alx-uta/RC-Transmitter/3D/STEP/Battery/BatteryCover.step

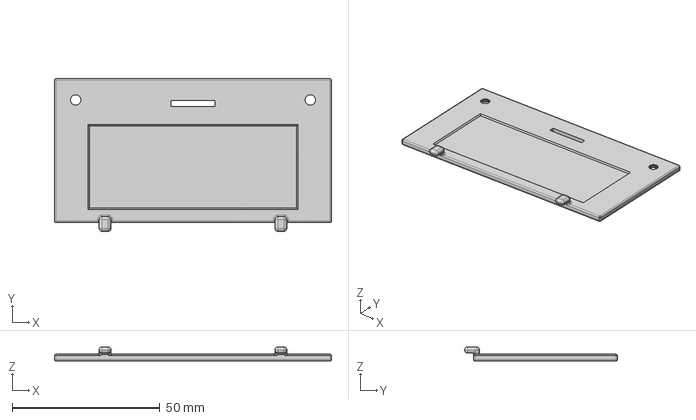
[picture p15: CAD file, 2024-01-06]
3D/STEP/Battery/BatteryCover.step
93.7 x 51.7 x 4.85 mm
