alx-uta/RC-Transmitter/3D/STEP/Battery/21700_BatteryHolder.step

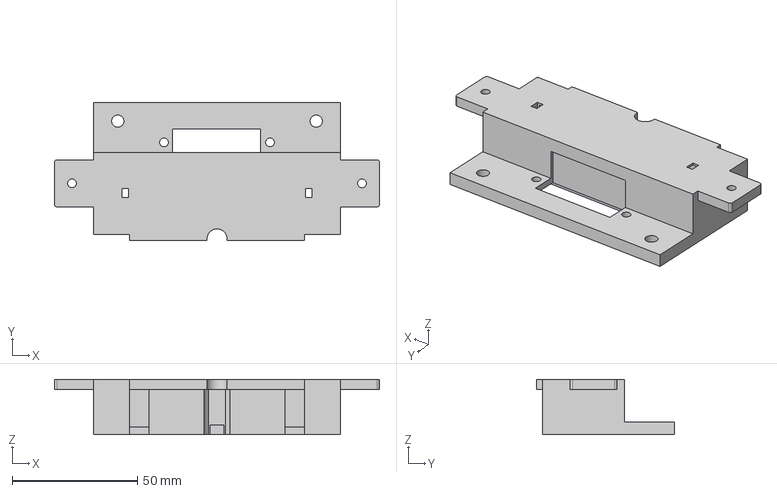
[picture p16: CAD file, 2024-01-06]
3D/STEP/Battery/21700_BatteryHolder.step
130.0 x 55.0 x 22.0 mm
