alx-uta/RC-Transmitter/3D/STEP/Battery/18650_BatteryHolderSpacer.step

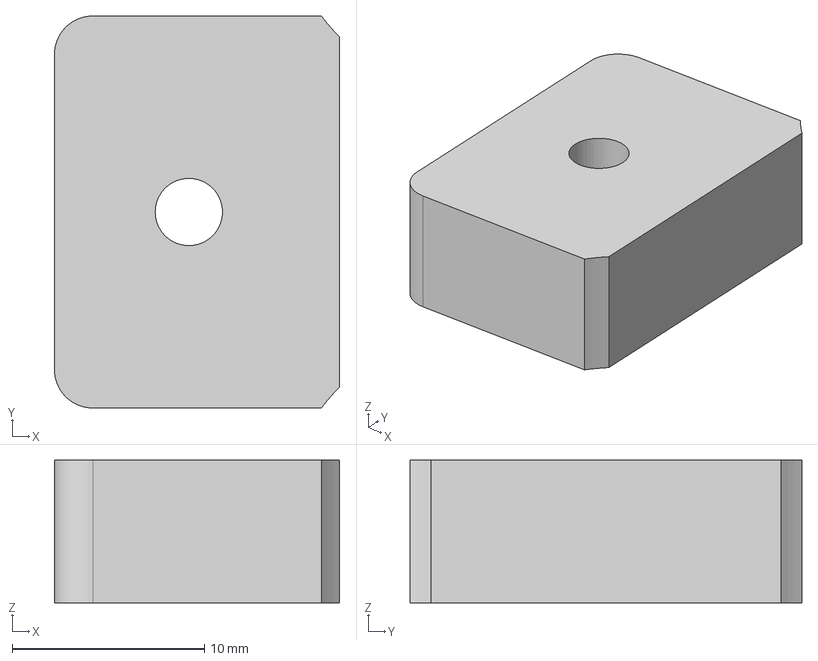
[picture p17: CAD file, 2024-01-06]
3D/STEP/Battery/18650_BatteryHolderSpacer.step
14.8 x 20.4 x 7.44 mm
