alx-uta/RC-Transmitter/3D/STEP/Battery/18650_BatteryHolder.step

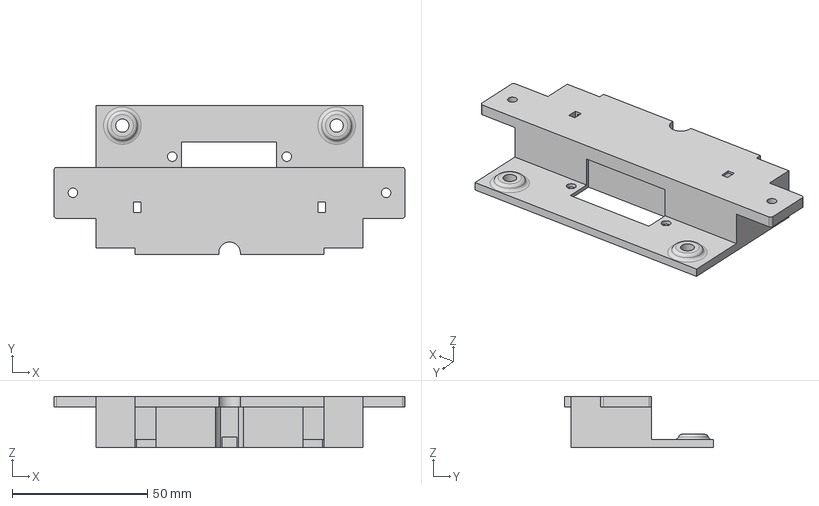
[picture p18: CAD file, 2024-01-06]
3D/STEP/Battery/18650_BatteryHolder.step
130.0 x 55.0 x 19.0 mm
