alx-uta/RC-Transmitter/code/RemoteTx/src/tx/tx_data.cpp

/**
 * RC Transmitter – ESP32 / SX1280
 * https://github.com/alx-uta/RC-Transmitter
 * 
 * Alex Uta
 * microknot.dev
 */

#include "tx.hpp"
#include <algorithm> // for std::min

/**
 * Read the data for the joysticks
 */
void Tx::joysticks() {
    int16_t
        joystick_x1_1, joystick_x1_2,
        joystick_y1_1, joystick_y1_2,
        joystick_x2_1, joystick_x2_2,
        joystick_y2_1, joystick_y2_2;
    uint8_t
        x1,
        y1,
        x2,
        y2,
        joystick_x1_map,
        joystick_y1_map,
        joystick_x2_map,
        joystick_y2_map;

    const uint8_t joysticks_num_channels = 8;
    uint8_t joysticks_channels[joysticks_num_channels] = {
        _config.LEFT_JOYSTICK_X_1,
        _config.LEFT_JOYSTICK_X_2,

        _config.LEFT_JOYSTICK_Y_1,
        _config.LEFT_JOYSTICK_Y_2,

        _config.RIGHT_JOYSTICK_X_1,
        _config.RIGHT_JOYSTICK_X_2,

        _config.RIGHT_JOYSTICK_Y_1,
        _config.RIGHT_JOYSTICK_Y_2
    };

    // Joysticks Values
    int16_t readings[joysticks_num_channels];
    _joystick.analogReadMultiple(
        joysticks_channels, joysticks_num_channels, readings
    );

    joystick_x1_1 = readings[_config.LEFT_JOYSTICK_X_1];
    joystick_x1_2 = readings[_config.LEFT_JOYSTICK_X_2];

    joystick_y1_1 = readings[_config.LEFT_JOYSTICK_Y_1];
    joystick_y1_2 = readings[_config.LEFT_JOYSTICK_Y_2];

    joystick_x2_1 = readings[_config.RIGHT_JOYSTICK_X_1];
    joystick_x2_2 = readings[_config.RIGHT_JOYSTICK_X_2];

    joystick_y2_1 = readings[_config.RIGHT_JOYSTICK_Y_1];
    joystick_y2_2 = readings[_config.RIGHT_JOYSTICK_Y_2];

    // Left joystick
    joystick_x1_map = this->joystickMap(
        (joystick_x1_1+joystick_x1_2)/2,
        _config.left_joystick_min_value_x + _config.left_joystick_drift_value_x,
        _config.left_joystick_max_value_x - _config.left_joystick_drift_value_x,
        _config.left_joystick_middle_value_x,
        _config.joystick_default_value,
        _config.joystick_min_out,
        _config.joystick_max_out
    );
    joystick_y1_map = this->joystickMap(
        (joystick_y1_1+joystick_y1_2)/2,
        _config.left_joystick_min_value_y + _config.left_joystick_drift_value_y,
        _config.left_joystick_max_value_y - _config.left_joystick_drift_value_y,
        _config.left_joystick_middle_value_y,
        _config.joystick_default_value,
        _config.joystick_min_out,
        _config.joystick_max_out
    );

    // Right Joystick
    joystick_x2_map = this->joystickMap(
        (joystick_x2_1+joystick_x2_2)/2,
        _config.right_joystick_min_value_x + _config.right_joystick_drift_value_x,
        _config.right_joystick_max_value_x - _config.right_joystick_drift_value_x,
        _config.right_joystick_middle_value_x,
        _config.joystick_default_value,
        _config.joystick_min_out,
        _config.joystick_max_out
    );
    joystick_y2_map = this->joystickMap(
        (joystick_y2_1+joystick_y2_2)/2,
        _config.right_joystick_min_value_y + _config.right_joystick_drift_value_y,
        _config.right_joystick_max_value_y - _config.right_joystick_drift_value_y,
        _config.right_joystick_middle_value_y,
        _config.joystick_default_value,
        _config.joystick_min_out,
        _config.joystick_max_out
    );

    /**
     * Set the payload accounting for the drift value
     */
    // Left Joystick
    x1 = this->applyJoystickThreshold(
        (joystick_x1_1+joystick_x1_2)/2,
        _config.left_joystick_middle_value_x,
        _config.left_joystick_drift_value_x,
        joystick_x1_map
    );
    y1 = this->applyJoystickThreshold(
        (joystick_y1_1+joystick_y1_2)/2,
        _config.left_joystick_middle_value_y,
        _config.left_joystick_drift_value_y,
        joystick_y1_map
    );

    // Right Joystick
    x2 = this->applyJoystickThreshold(
        (joystick_x2_1+joystick_x2_2)/2,
        _config.right_joystick_middle_value_x,
        _config.right_joystick_drift_value_x,
        joystick_x2_map
    );
    y2 = this->applyJoystickThreshold(
        (joystick_y2_1+joystick_y2_1)/2,
        _config.right_joystick_middle_value_y,
        _config.right_joystick_drift_value_y,
        joystick_y2_map
    );

    this->setLeftJoystick(x1, y1);
    this->setRightJoystick(x2, y2);
}


/**
 * Read the data for the potentiometers
 */
void Tx::potentiometers() {
    int
        // Potentiometer Last Value
        pot1LastValue, pot2LastValue, pot3LastValue, pot4LastValue, pot5LastValue, pot6LastValue,
        potLastValue;
        
        const uint8_t potentiometers_num_channels = 6;
        uint8_t potentiometers_channels[potentiometers_num_channels] = {
            _config.POTENTIOMETER_1_ADC,
            _config.POTENTIOMETER_2_ADC,
            _config.POTENTIOMETER_3_ADC,
            _config.POTENTIOMETER_4_ADC,
            _config.POTENTIOMETER_5_ADC,
            _config.POTENTIOMETER_6_ADC
        };

    // Potentiometer Values
    int16_t readings[potentiometers_num_channels];
    _potentiometer.analogReadMultiple(potentiometers_channels, potentiometers_num_channels, readings);

    // Prevent jumping values
    const int numPots = 6;

    int potValues[numPots] = {
        readings[_config.POTENTIOMETER_1_ADC],
        readings[_config.POTENTIOMETER_2_ADC],
        readings[_config.POTENTIOMETER_3_ADC],
        readings[_config.POTENTIOMETER_4_ADC],
        readings[_config.POTENTIOMETER_5_ADC],
        readings[_config.POTENTIOMETER_6_ADC]
    };
    int potLastValues[numPots] = {pot1LastValue, pot2LastValue, pot3LastValue, pot4LastValue, pot5LastValue, pot6LastValue};

    for (int i = 0; i < numPots; ++i) {
        int diff = abs(potLastValues[i] - potValues[i]);
        if (diff > _config.pot_drift_value) {
            if (potValues[i] > _config.pot_max) {
                potLastValues[i] = _config.pot_max;
            } else {
                potLastValues[i] = potValues[i];
            }
        }
    }

    // Set the payload
    for (int i = 0; i < 6; ++i) {
        potLastValues[i] = map(potLastValues[i], _config.pot_min, _config.pot_max, _config.pot_min, _config.pot_out_max);
    }

    this->setPotentiometers(
        potLastValues[0],
        potLastValues[1],
        potLastValues[2],
        potLastValues[3],
        potLastValues[4],
        potLastValues[5]
    );
}


/**
 * Read the data for the rotary encoders
 */
void Tx::readMCP23S17() {
    uint16_t pin_state_encoders = _rotaryRead.read16();

    // Get and set the encoder position
    if (this->leftAnoRotaryEncoderPosition >= _config.encoder_min && this->leftAnoRotaryEncoderPosition <= _config.encoder_max) {
        this->leftAnoRotaryEncoderPosition -= _leftRotary.encoderDirection(
            (pin_state_encoders & (1 << _config.rotary_encoder_1_enc_b)) != 0,
            (pin_state_encoders & (1 << _config.rotary_encoder_1_enc_a)) != 0
        );

        this->rightAnoRotaryEncoderPosition -= _rightRotary.encoderDirection(
            (pin_state_encoders & (1 << _config.rotary_encoder_2_enc_b)) != 0,
            (pin_state_encoders & (1 << _config.rotary_encoder_2_enc_a)) != 0
        );
    }

    // Update the encoder position
    this->setAnoRotaryEncoderLeftPosition(
        (uint8_t)(this->leftAnoRotaryEncoderPosition >> 8),
        (uint8_t)this->leftAnoRotaryEncoderPosition
    );

    this->setAnoRotaryEncoderRightPosition(
        (uint8_t)(this->rightAnoRotaryEncoderPosition >> 8),
        (uint8_t)this->rightAnoRotaryEncoderPosition
    );

    // pin_state_encoders
    uint16_t pin_state_switches = _switches.read16();
    this->setSwitchesPushButtons(
        pin_state_encoders,
        pin_state_switches
    );
}
