alx-uta/RC-Transmitter/code/RemoteRx/example.user_config.hpp

/**
 * RC Transmitter – ESP32 / SX1280
 * https://github.com/alx-uta/RC-Transmitter
 *
 * Alex Uta
 * microknot.dev
 */

#ifndef USER_CONFIG_HPP
#define USER_CONFIG_HPP

// Debug
#define ENABLE_SERIAL_PRINT     true
#define ENABLE_DEBUG            false
#define ENABLE_RADIO_LIB_DEBUG  false

/**
 * Battery
 */
float BATTERY_MIN = 1.5; // 3 / 2 = 1.5, with a min of 3V
float BATTERY_MAX = 2.1; // 4.2 / 2 = 4.2v, with a max of 4.2V

/**
 * SX1280
 */

/*!
  \brief No shaping.
*/
#define RADIOLIB_SHAPING_NONE                                   (0x00)

/*!
  \brief Gaussian shaping filter, BT = 0.5
*/
#define RADIOLIB_SHAPING_0_5                                    (0x02)

/*!
  \brief Gaussian shaping filter, BT = 1.0
*/
#define RADIOLIB_SHAPING_1_0                                    (0x04)


// This needs to be the same as the Remote TX
float   SX1280_FREQUENCY                    = 2410; // Remote TX
float   SX1280_TX_FREQUENCY                 = 2420; // External TX
int     SX1280_FREQUENCY_DEVIATION          = 200;
int     SX1280_BIT_RATE                     = 250;
int     SX1280_OUTPUT_POWER                 = 8; // -18 to 13 dBm
int     SX1280_GAIN_CONTROL                 = 8; // 1 - 13
uint8_t SX1280_DATA_SHAPING                 = RADIOLIB_SHAPING_0_5;
int     SX1280_CRC_VALUE                    = 1;
int     SX1280_PREAMBLE_LENGTH              = 4;
bool    SX1280_SET_HIGH_SENSITIVITY_MODE    = true;

int SX1280_HOPPING_INTERNAL_MILLIS          = 3000;
int SX1280_TX_FREQUENCY_AVAILABILITY_MILLIS = 5;

// Binding Key
bool BINDING_KEY[16] = {
    0, 0, 0, 0, 0, 0, 0, 0,
    0, 0, 0, 0, 0, 0, 0, 0
};

#endif  // USER_CONFIG_HPP
